DuncanB6/foghorn/admin/Media/IMG_7396.JPG

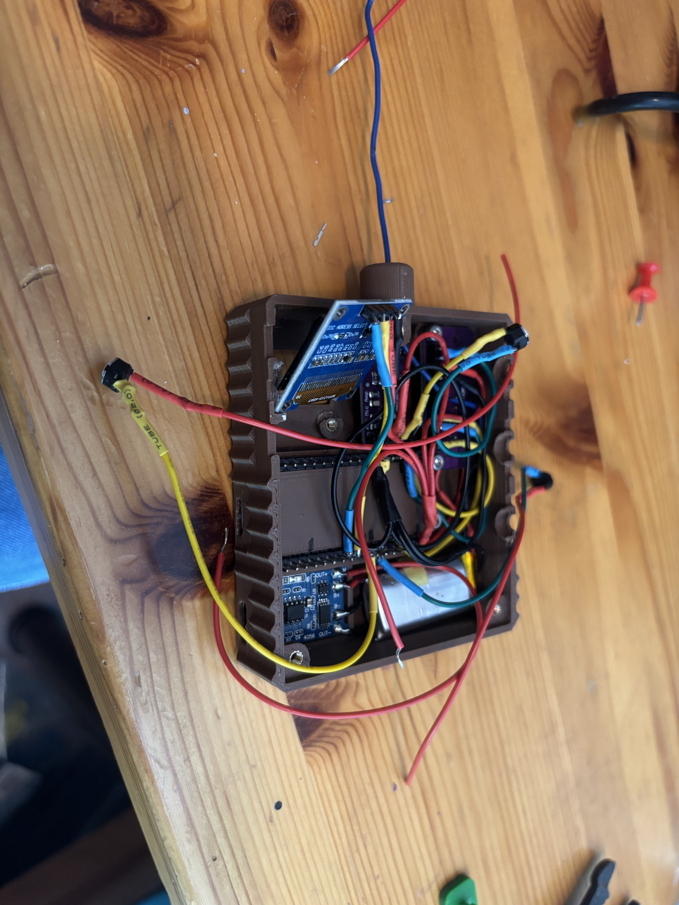
admin/Media/IMG_7396.JPG
