DuncanB6/foghorn/admin/Media/IMG_7399.JPG

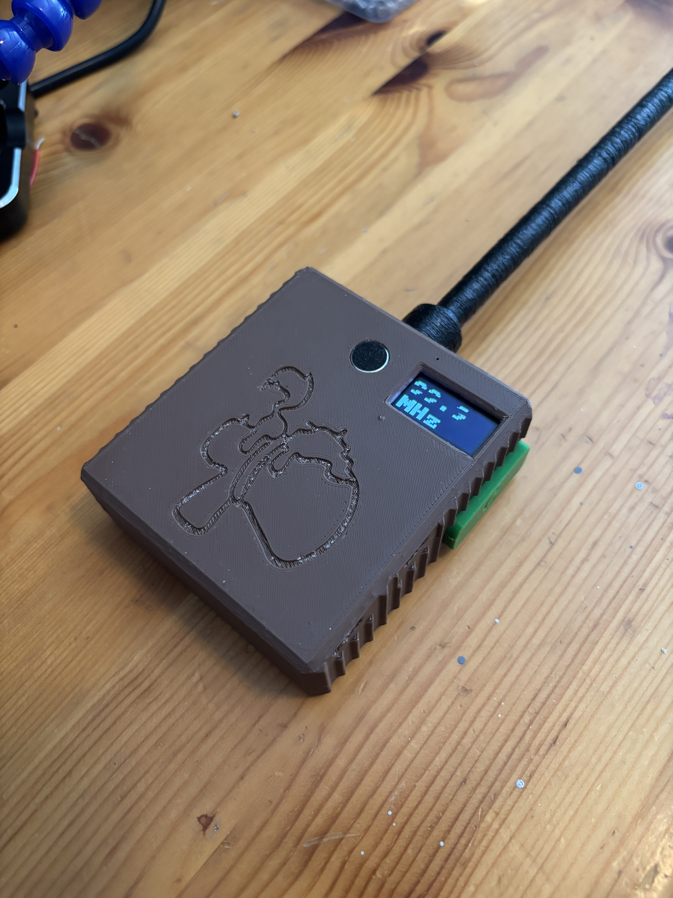
admin/Media/IMG_7399.JPG
